Evanston09/skyprint/src/aircraft_client.cpp

#include "aircraft_client.h"

#include <Arduino.h>
#include <HTTPClient.h>
#include <WiFi.h>
#include <WiFiClientSecure.h>

#include <ctime>

#include "adsblol_ca.h"
#include "aircraft_json.h"
#include "settings.h"

namespace skyprint {

// Let’s Encrypt Root YR from
// https://letsencrypt.org/certs/gen-y/root-yr.pem. ADSB.lol is issued through
// YR1; trusting YR directly avoids the longer X1 cross-sign path that can
// exceed the practical TLS limits of older embedded clients.
const char kAdsbLolRootCa[] PROGMEM = R"CERT(
-----BEGIN CERTIFICATE-----
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
sI1ANRYvqSFC2X1VRZfDg+wD6E21BccmifG4yWc=
-----END CERTIFICATE-----
)CERT";

FetchResult AdsbLolClient::fetchNearby(double latitude, double longitude,
                                       double radiusNm) const {
  FetchResult result;
  if (std::time(nullptr) < 1700000000) {
    result.failure = FetchFailure::kClock;
    result.error = "clock is not synchronized; TLS verification deferred";
    return result;
  }

  String url = settings::kApiBaseUrl;
  url += "/";
  url += String(latitude, 6);
  url += "/";
  url += String(longitude, 6);
  url += "/";
  url += String(radiusNm, 0);

  // Resolve separately so DNS failures are not flattened into HTTPClient's
  // generic "connection refused" error. Connecting to the resolved address
  // with the hostname argument preserves SNI and certificate verification.
  IPAddress apiAddress;
  if (!WiFi.hostByName(settings::kApiHostname, apiAddress)) {
    result.failure = FetchFailure::kDns;
    result.error = std::string("DNS lookup failed for ") +
                   settings::kApiHostname;
    return result;
  }

  WiFiClientSecure secureClient;
  secureClient.setCACert(kAdsbLolRootCa);
  secureClient.setHandshakeTimeout(settings::kTlsHandshakeTimeoutSeconds);
  if (!secureClient.connect(apiAddress, settings::kApiPort,
                            settings::kApiHostname, kAdsbLolRootCa, nullptr,
                            nullptr)) {
    result.failure = FetchFailure::kConnection;
    result.error = "TLS connection failed";
    char tlsError[128] = {};
    const int tlsErrorCode = secureClient.lastError(tlsError, sizeof(tlsError));
    if (tlsErrorCode < 0) {
      result.error += std::string(": ") + std::to_string(tlsErrorCode) +
                      " (" + tlsError + ")";
    }
    return result;
  }

  HTTPClient http;
  http.setConnectTimeout(settings::kHttpConnectTimeoutMs);
  http.setTimeout(settings::kHttpResponseTimeoutMs);
  http.useHTTP10(true);
  if (!http.begin(secureClient, url)) {
    result.failure = FetchFailure::kConnection;
    result.error = "could not initialize HTTPS request";
    return result;
  }
  http.setUserAgent("Skyprint/1.0 personal-aircraft-display");
  http.addHeader("Accept", "application/json");
  http.addHeader("Accept-Encoding", "identity");

  result.httpStatus = http.GET();
  if (result.httpStatus != HTTP_CODE_OK) {
    result.failure = result.httpStatus < 0 ? FetchFailure::kConnection
                                          : FetchFailure::kHttp;
    result.error = result.httpStatus < 0
                       ? std::string("HTTPS request failed: ") +
                             http.errorToString(result.httpStatus).c_str()
                       : std::string("ADSB.lol returned HTTP ") +
                             std::to_string(result.httpStatus);
    http.end();
    return result;
  }

  if (!parseAircraftJson(http.getStream(), latitude, longitude, radiusNm,
                         result.aircraft, result.error)) {
    result.failure = FetchFailure::kJson;
    http.end();
    return result;
  }

  result.success = true;
  http.end();
  return result;
}

}  // namespace skyprint
